IIBM/impedance-correction/Informe proyecto/datos.tex

%||||||||||||||||||||||||||||||||||||||||||||||||||||||||||||||||||||||||||||||%
%|||||||||||||||||||||||||||||| Datos del informe |||||||||||||||||||||||||||||%
%||||||||||||||||||||||||||||||||||||||||||||||||||||||||||||||||||||||||||||||%
\newcommand\codmateria{66.09/86.07}
\newcommand\nommateria{Laboratorio de Microcomputadoras}
\newcommand\turno{1 (Martes 19 a 22 hs)}
\newcommand\docente{Stola, Gerardo}
\newcommand\autores{Cassani - Ferrari Bihurriet - Gomez}
\newcommand\anio{2015}
\newcommand\cuatrim{Segundo}
\newcommand\titulo{Corrector de impedancia de electrodos}
\newcommand\fecha{\today}
\newcommand\integrantes{ % \integrante{Apellido}{Nombre}{padrón}
    \integrante{Cassani}{María Victoria}{95.145}
    \integrante{Ferrari Bihurriet}{Francisco}{92.275}
    \integrante{Gomez}{Kevin Leonel}{93.906}
}
% Descomentar para mostrar el índice
\newcommand\indice{}
% Directorio de imágenes
\newcommand\imgdir{./img}
