IIBM/impedance-correction/Esquemático/Esquemático.asc

C1: cap; 47n
C2: cap; 4.7n
C3: cap; 4.7n
C4: cap; 47n
C5: cap; 47n
C6: cap; 4.7n
C7: cap; 4.7n
C8: cap; 100n
C9: cap; 1n
C10: cap; 1µ
C11: cap; 100n
C12: cap; 1µ
C13: cap; 100n
R1: res; 100
R2: res; 100k
R3: res; 470k
R4: res; 10k
R5: res; 10k
R6: res; 10k
R7: res; 1k
R8: res; 33k
R9: res; 33k
R10: res; 2.2k
R11: res; 2.2k
R12: res; 100k
R13: res; 1k
R14: res; 1k
R15: res; 22k
R16: res; 100k
R17: res; 10k
R20: res; 33k
R21: res; 33k
R22: res; 2.2k
R23: res; 2.2k
R24: res; 1k
R25: res; 1.2Meg
Ra: res; 100k
Rb: res; 100k
Relectrodo: res; 20m
U1: UniversalOpamp2; Avol=1Meg GBW=80Meg Slew=10Meg; ilimit=25m rail=0 Vos=20u phimargin=45
U2: UniversalOpamp2; Avol=1Meg GBW=80Meg Slew=10Meg; ilimit=25m rail=0 Vos=20u phimargin=45
U3: UniversalOpamp2; Avol=1Meg GBW=80Meg Slew=10Meg; ilimit=25m rail=0 Vos=20u phimargin=45
U4: UniversalOpamp2; Avol=1Meg GBW=80Meg Slew=10Meg; ilimit=25m rail=0 Vos=-20u phimargin=45
U5: UniversalOpamp2; Avol=1Meg GBW=80Meg Slew=10Meg; ilimit=25m rail=0 Vos=20u phimargin=45
U6: UniversalOpamp2; Avol=1Meg GBW=80Meg Slew=10Meg; ilimit=25m rail=0 Vos=20u phimargin=45
U7: UniversalOpamp2; Avol=1Meg GBW=80Meg Slew=10Meg; ilimit=25m rail=0 Vos=20u phimargin=45
U8: UniversalOpamp2; Avol=1Meg GBW=80Meg Slew=10Meg; ilimit=25m rail=0 Vos=20u phimargin=45
V1: voltage; 5
Vcte: voltage; 3
Vsen1: voltage; PULSE(0 5 0 12.49u 5n 5n 12.5u)
Vsen2: voltage; PULSE(0 5 0 12.49u 5n 5n 12.5u)
Vsen: voltage; SINE(2.5 2 1kHz)
Named nets: Vcc, 0, Vcc/2, ADC, offset, ADC_off
.tran 0 300m 0 10u
*** R3: Multiplexor ***
 
200 nA => 470 k-ohm
120 nA => 820 k-ohm
  80 nA => 1.2 Meg-ohm
  30 nA => 3.3 Meg-ohm
